vishalsaravanan-k/home-automation-using-esp32-and-relay/Images/1.png

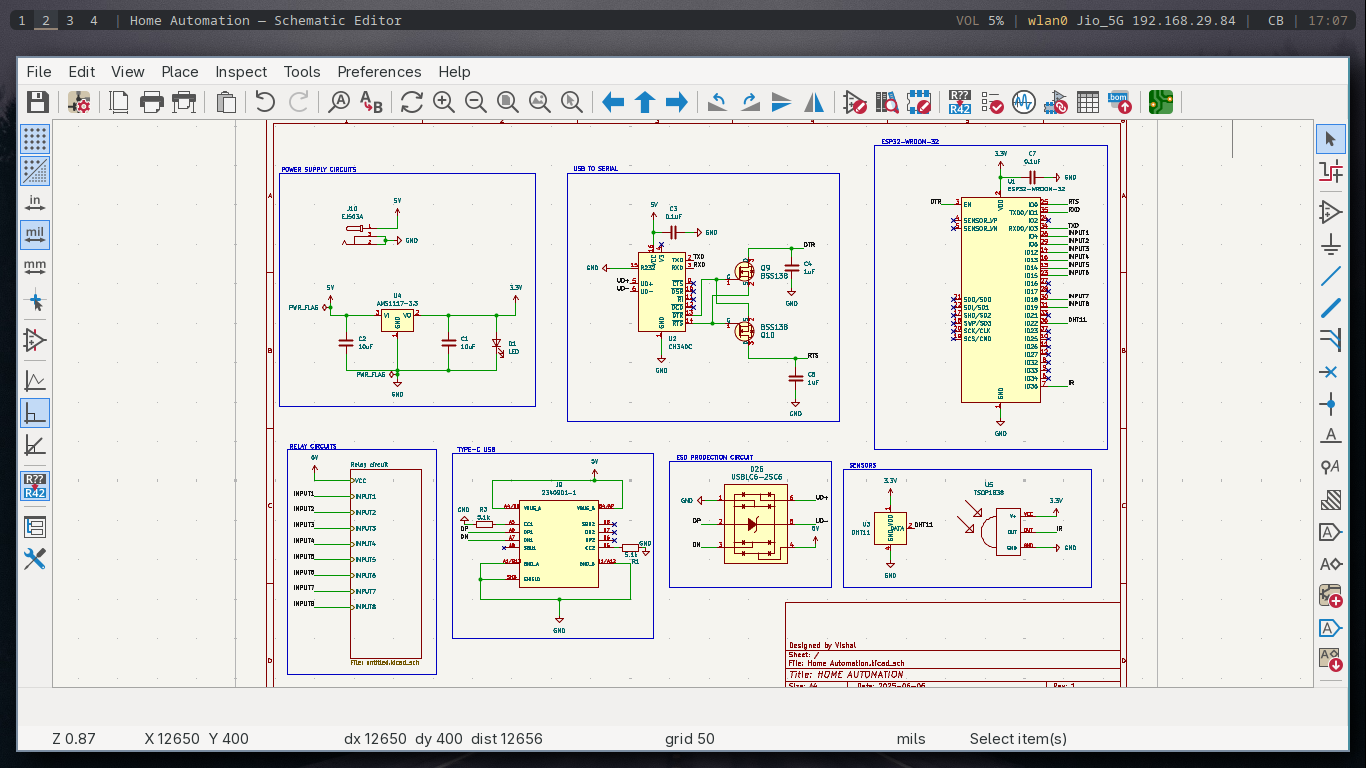
Images/1.png
