vishalsaravanan-k/home-automation-using-esp32-and-relay/Images/2.png

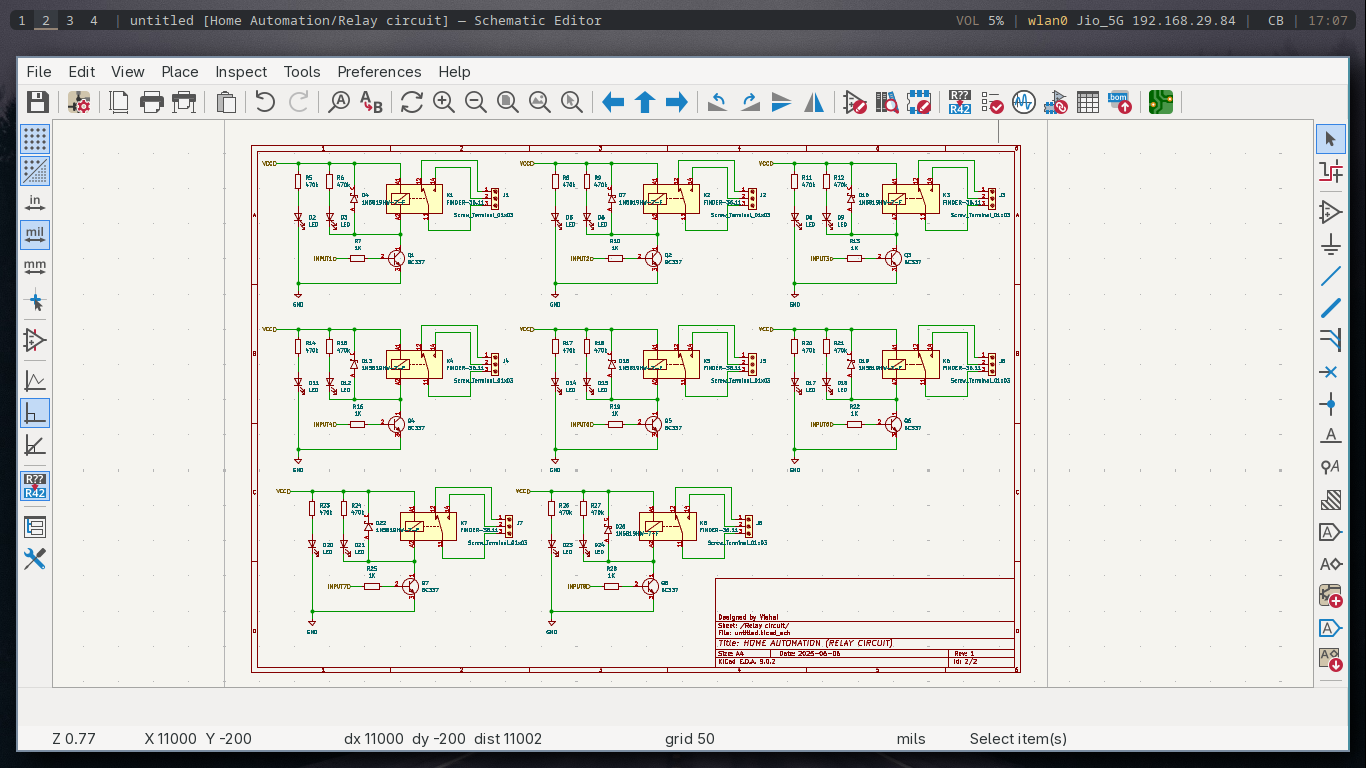
Images/2.png
