vishalsaravanan-k/home-automation-using-esp32-and-relay/Images/3.png

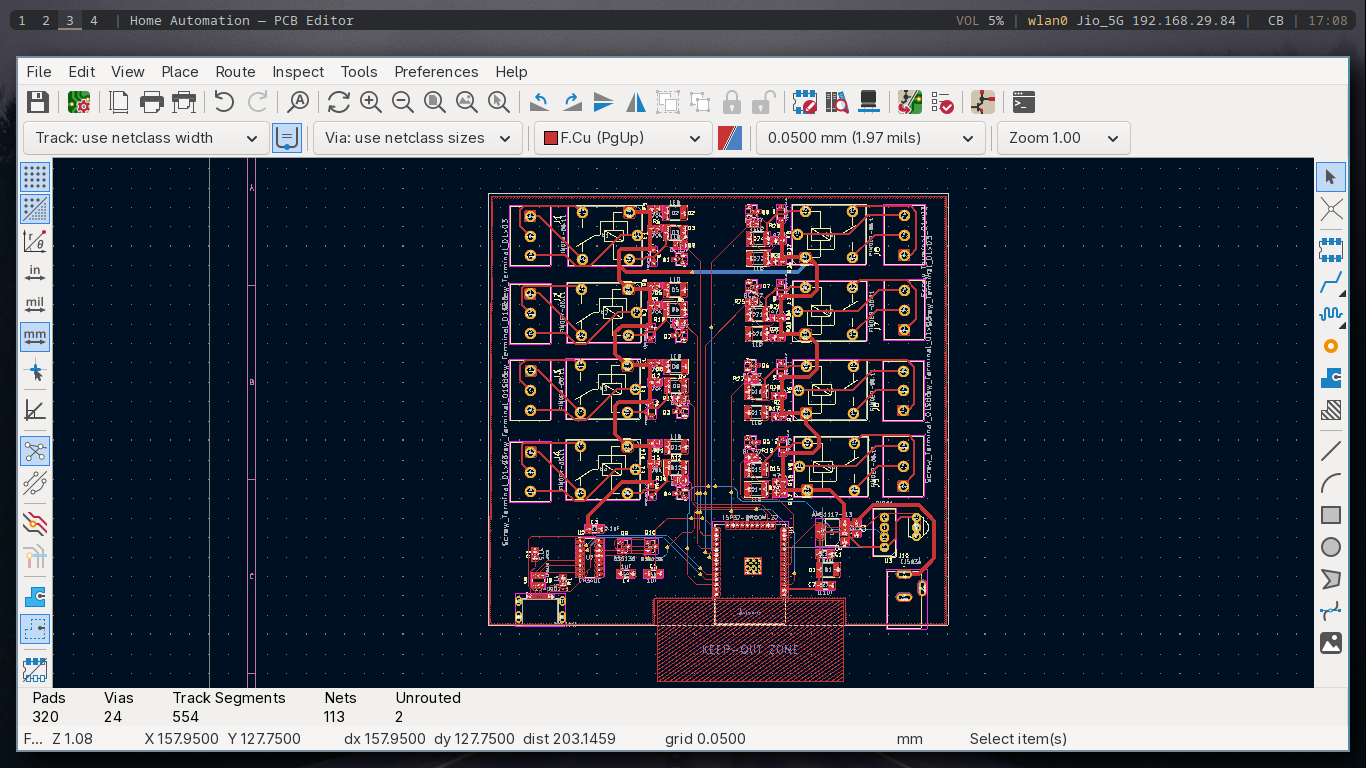
Images/3.png
