vishalsaravanan-k/home-automation-using-esp32-and-relay/Images/4.png

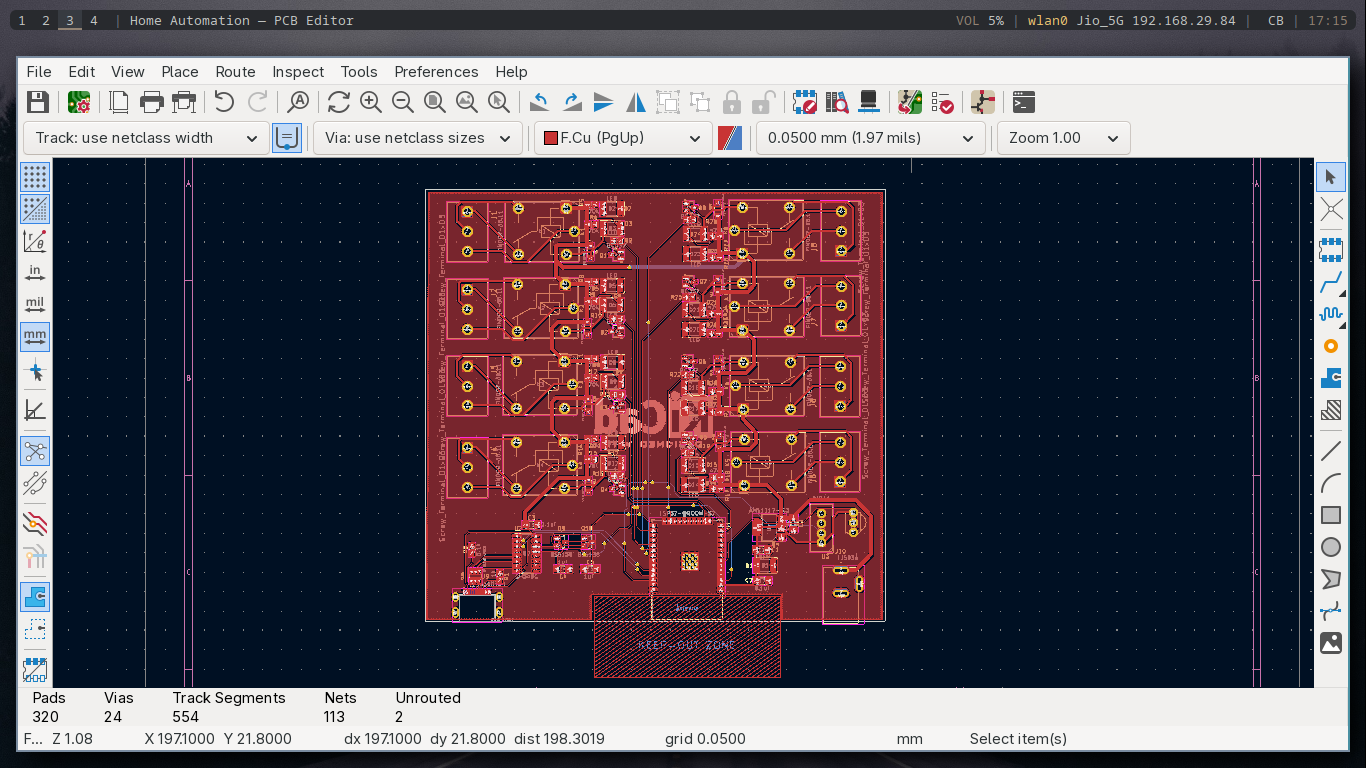
Images/4.png
