vishalsaravanan-k/home-automation-using-esp32-and-relay/Images/6.png

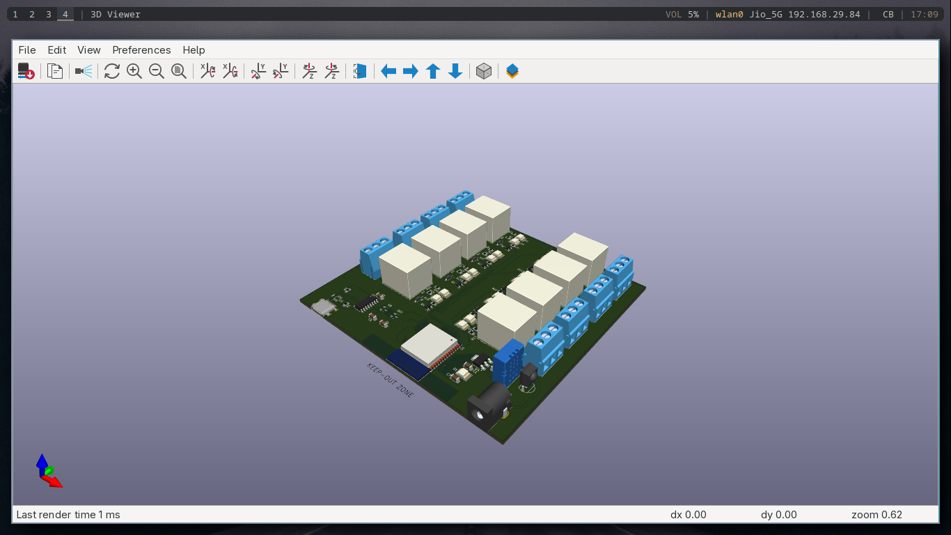
Images/6.png
