vishalsaravanan-k/home-automation-using-esp32-and-relay/Images/7.png

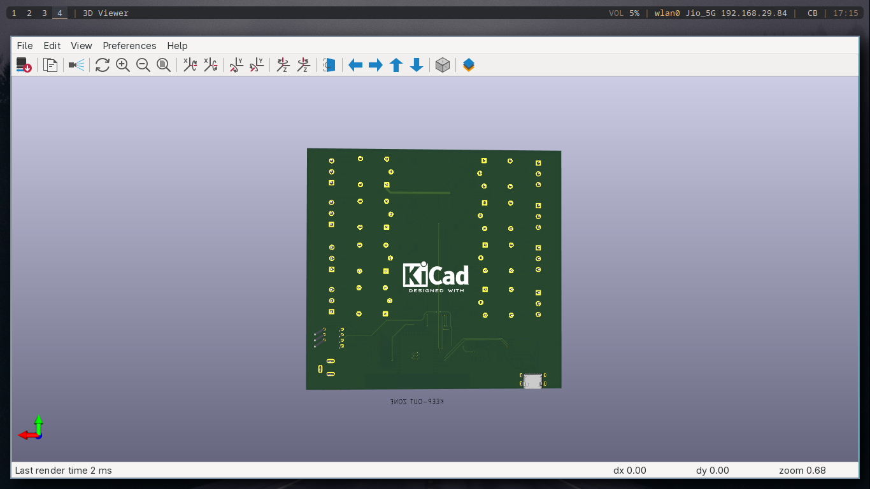
Images/7.png
